blackjetrock/pico-sp0256/firmware/allophoneDefs.h

//                                                                                                                              
//Allophone Defines
//                                                                                                                              
#define PA1    0
#define PA2    1
#define PA3    2
#define PA4    3
#define PA5    4
#define OY    5
#define AY    6
#define EH    7
#define KK3    8
#define PP    9
#define JH    10
#define NN1    11
#define NN     11
#define IH    12
#define TT2    13
#define RR1    14
#define RR     14
#define AX    15
#define MM    16
#define TT1    17
#define TT     17
#define DH1    18
#define DH     18
#define IY    19
#define EY    20
#define DD1    21
#define DD     21
#define UW1    22
#define UW     22
#define AO    23
#define AA    24
#define YY2    25
#define AE    26
#define HH1    27
#define HH     27
#define BB1    28
#define BB1    28
#define TH    29
#define UH    30
#define UW2    31
#define AW    32
#define DD2    33
#define GG3    34
#define VV    35
#define GG1    36
#define GG    36
#define SH    37
#define ZH    38
#define RR2    39
#define FF    40
#define KK2    41
#define KK1    42
#define KK     42
#define ZZ    43
#define NG    44
#define LL    45
#define WW    46
#define XR    47
#define WH    48
#define YY1    49
#define YY     49
#define CH    50
#define ER1    51
#define ER     51
#define ER2    52
#define OW    53
#define DH2    54
#define SS    55
#define NN2    56
#define HH2    57
#define OR    58
#define AR    59
#define YR    60
#define GG2    61
#define EL    62
#define BB2    63
